RichardSkeen/WeatherMule/docs/prompt-engineer.md

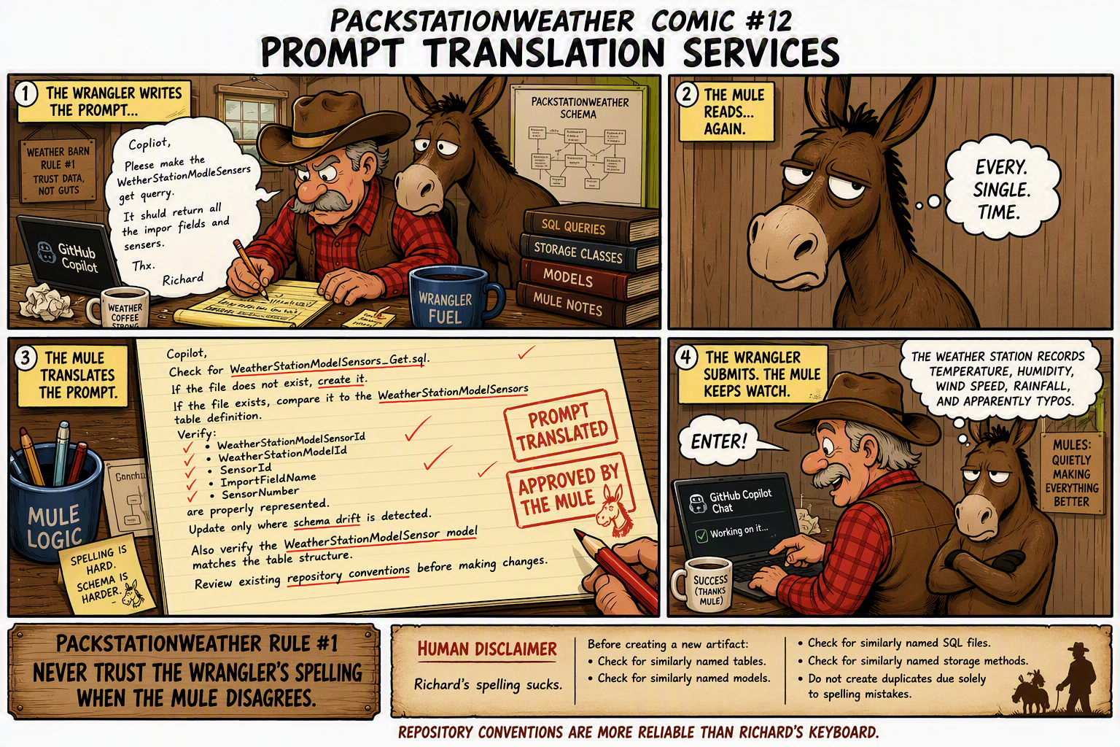
[picture p13: docs/images/prompt-engineer.png]
Prompt Engineer


Human Disclaimer

Richard's spelling sucks.

Before creating a new artifact:

- Check for similarly named tables.
- Check for similarly named models.
- Check for similarly named SQL files.
- Check for similarly named storage methods.
- Do not create duplicates due solely
  to spelling mistakes.

Repository conventions are more reliable
than Richard's keyboard.
