RichardSkeen/WeatherMule/Version.h

#pragma once

#define WeatherMule_Version "0.1.1"

//----------------------------------------------
// Prototypes
//---------------------------------------------- 


//----------------------------------------------
// Implementation below here
//---------------------------------------------- 
